kbranch/beefy_redox/STLs/LED Retainer.stl

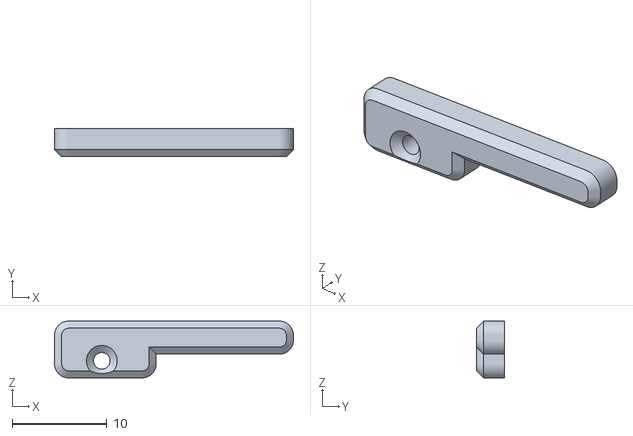
[picture p16: CAD file, 2020-09-06]
STLs/LED Retainer.stl
25.3 x 3.00 x 6.00
