kbranch/beefy_redox/STLs/Button Holder.stl

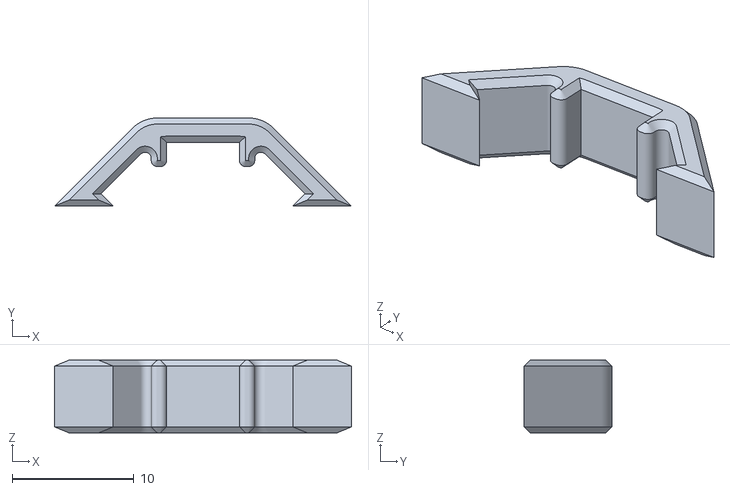
[picture p17: CAD file, 2020-09-06]
STLs/Button Holder.stl
24.4 x 7.25 x 6.00
