kbranch/beefy_redox/STLs/Keycaps/Keycap - 1.25U R3.stl

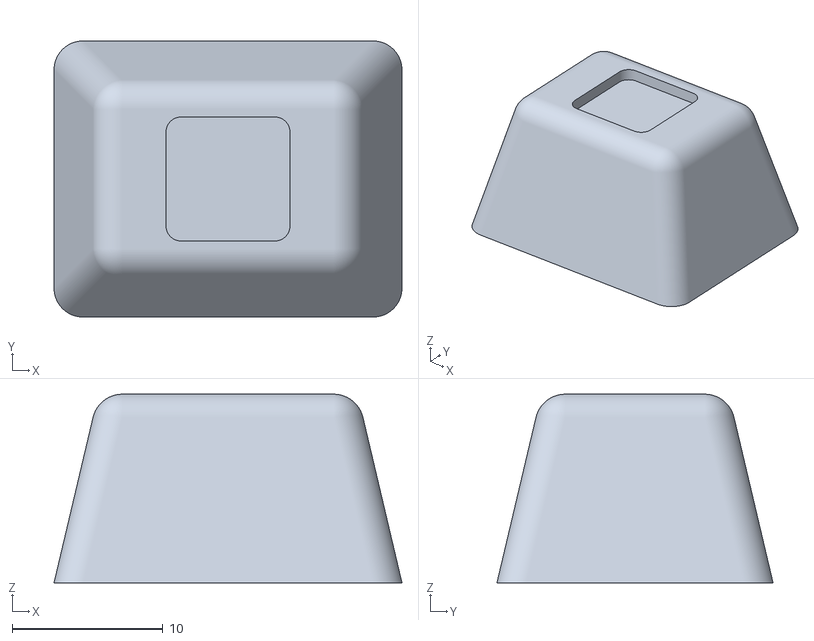
[picture p18: CAD file, 2020-09-06]
STLs/Keycaps/Keycap - 1.25U R3.stl
23.1 x 18.3 x 12.5
