kbranch/beefy_redox/STLs/Keycaps/Keycap - 1U R2.stl

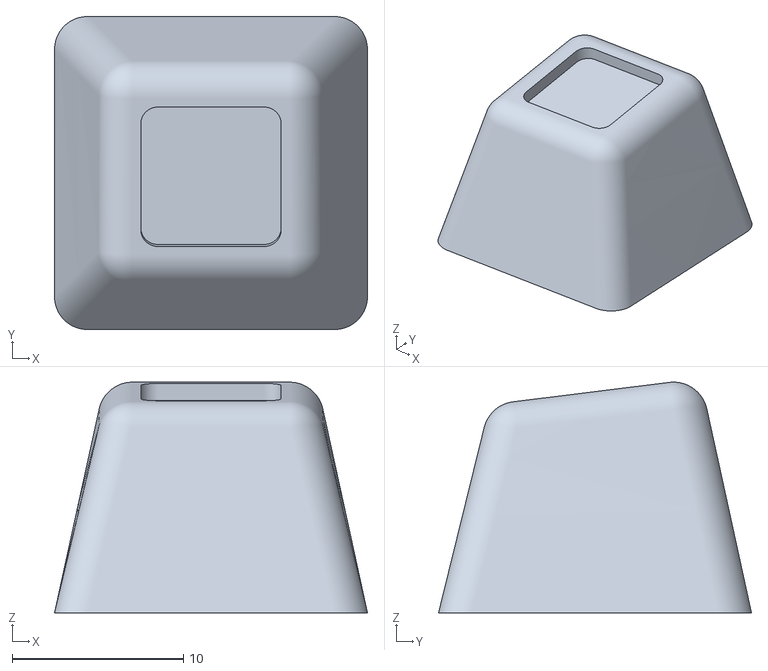
[picture p19: CAD file, 2020-09-06]
STLs/Keycaps/Keycap - 1U R2.stl
18.3 x 18.3 x 13.5
