kbranch/beefy_redox/STLs/Keycaps/Legends/Keycap - Legend Block - T.stl

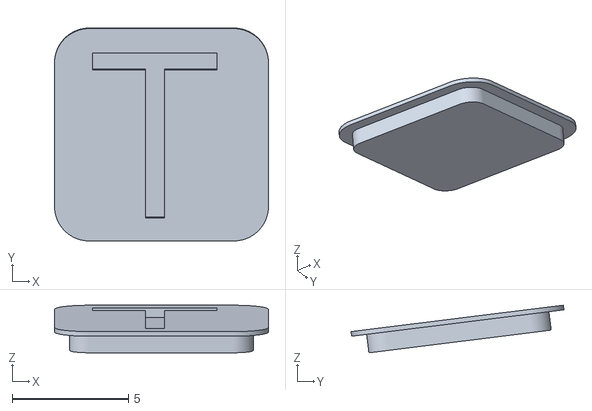
[picture p20: CAD file, 2020-09-06]
STLs/Keycaps/Legends/Keycap - Legend Block - T.stl
9.21 x 9.17 x 2.05
