kbranch/beefy_redox/STLs/Keycaps/Keycap - 1.5U R3.stl

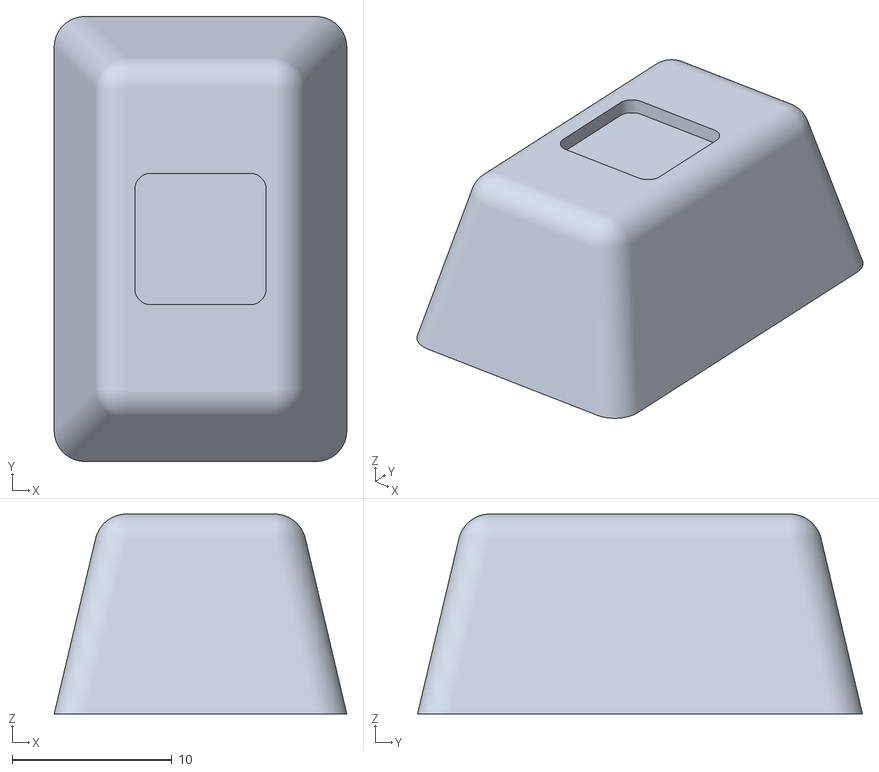
[picture p21: CAD file, 2020-09-06]
STLs/Keycaps/Keycap - 1.5U R3.stl
18.3 x 27.8 x 12.5
