kbranch/beefy_redox/STLs/Keycaps/Legends/Keycap - Part 5 - -.stl

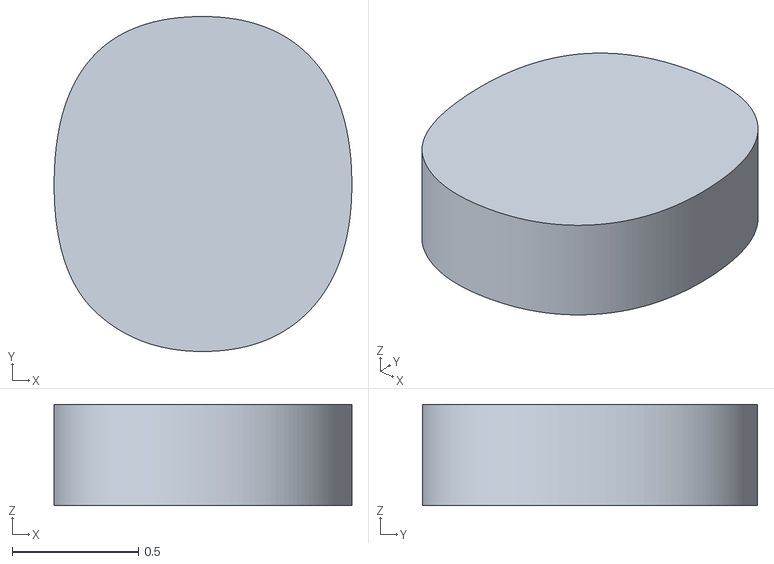
[picture p22: CAD file, 2020-09-06]
STLs/Keycaps/Legends/Keycap - Part 5 - -.stl
1.18 x 1.33 x 0.4
