kbranch/beefy_redox/STLs/Keycaps/Keycap - 1.25U R1.stl

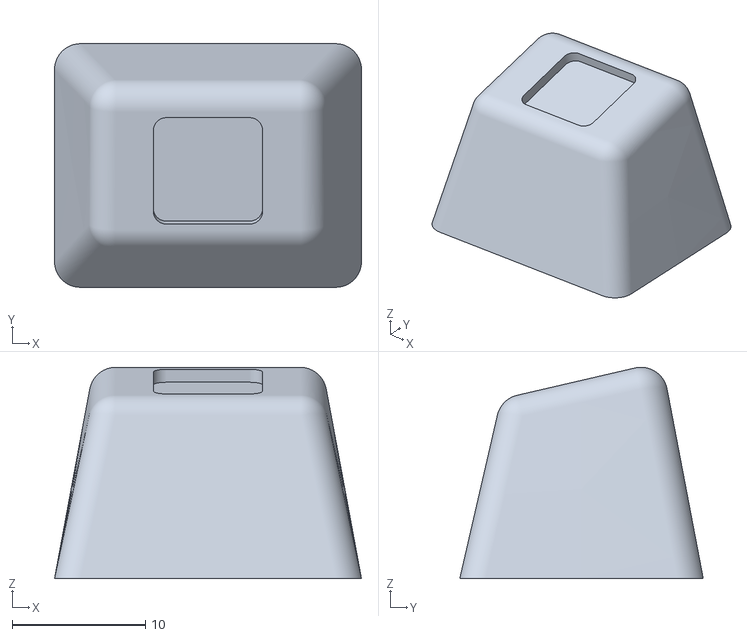
[picture p23: CAD file, 2020-09-06]
STLs/Keycaps/Keycap - 1.25U R1.stl
23.1 x 18.3 x 15.9
