kbranch/beefy_redox/STLs/Keycaps/Legends/Keycap - Part 3 - Space.stl

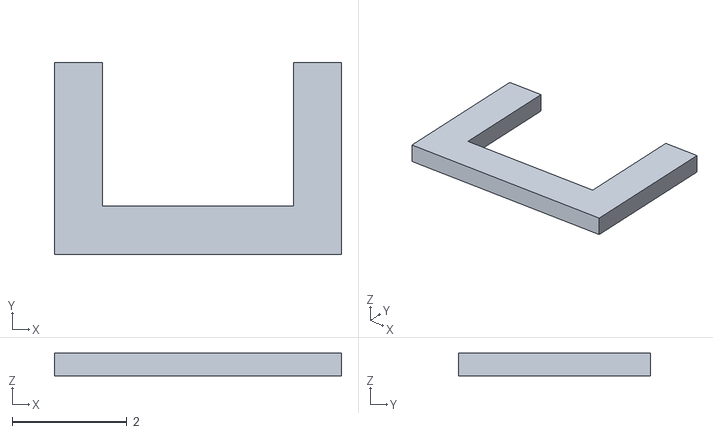
[picture p24: CAD file, 2020-09-06]
STLs/Keycaps/Legends/Keycap - Part 3 - Space.stl
5.00 x 3.34 x 0.4
