kbranch/beefy_redox/STLs/Keycaps/Legends/Keycap - Legend - 0.stl

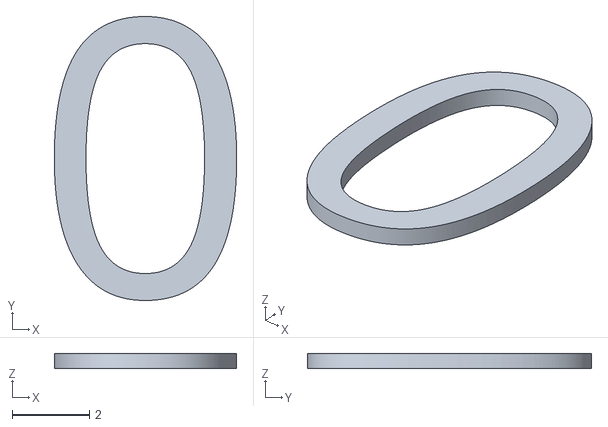
[picture p25: CAD file, 2020-09-06]
STLs/Keycaps/Legends/Keycap - Legend - 0.stl
4.73 x 7.36 x 0.4
