kbranch/beefy_redox/STLs/Keycaps/Legends/Keycap - Part 3 - Triangle.stl

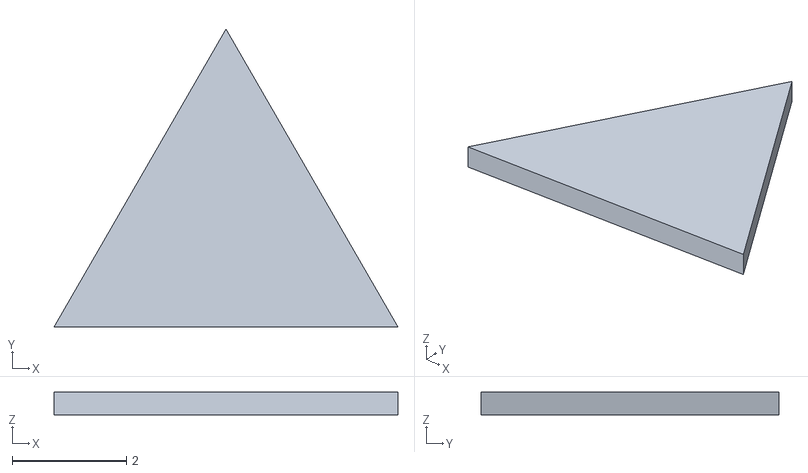
[picture p26: CAD file, 2020-09-06]
STLs/Keycaps/Legends/Keycap - Part 3 - Triangle.stl
6.02 x 5.21 x 0.4
