kbranch/beefy_redox/STLs/Keycaps/Legends/Keycap - Part 4 - Backslash.stl

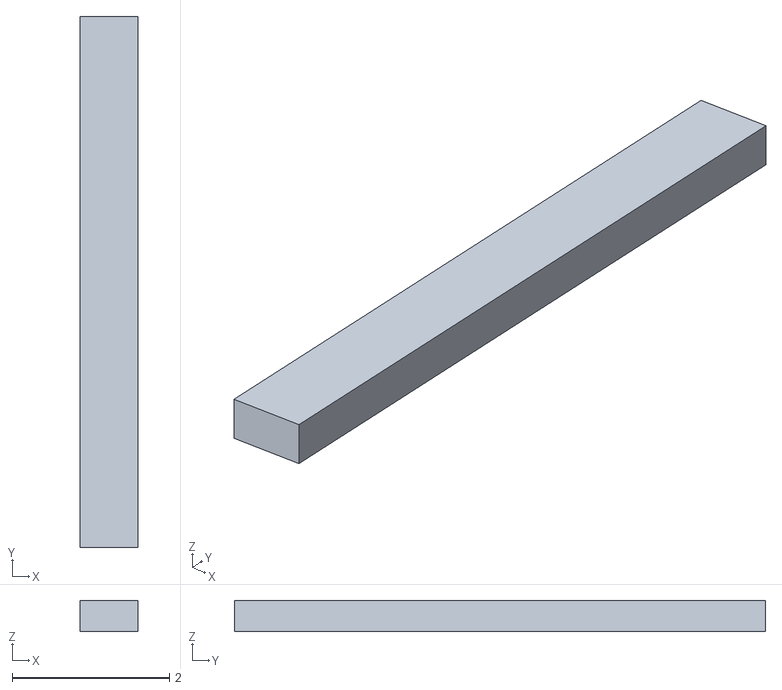
[picture p27: CAD file, 2020-09-06]
STLs/Keycaps/Legends/Keycap - Part 4 - Backslash.stl
0.733 x 6.74 x 0.4
