kbranch/beefy_redox/STLs/Keycaps/Legends/Keycap - Part 3 - Backspace.stl

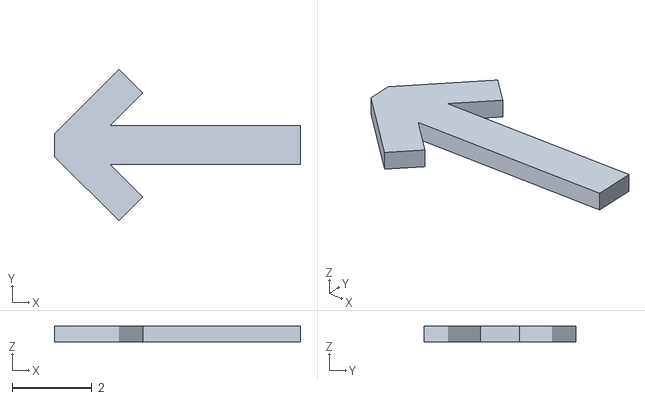
[picture p28: CAD file, 2020-09-06]
STLs/Keycaps/Legends/Keycap - Part 3 - Backspace.stl
6.18 x 3.82 x 0.4
