kbranch/beefy_redox/STLs/Keycaps/Legends/Keycap - Legend - Backslash.stl

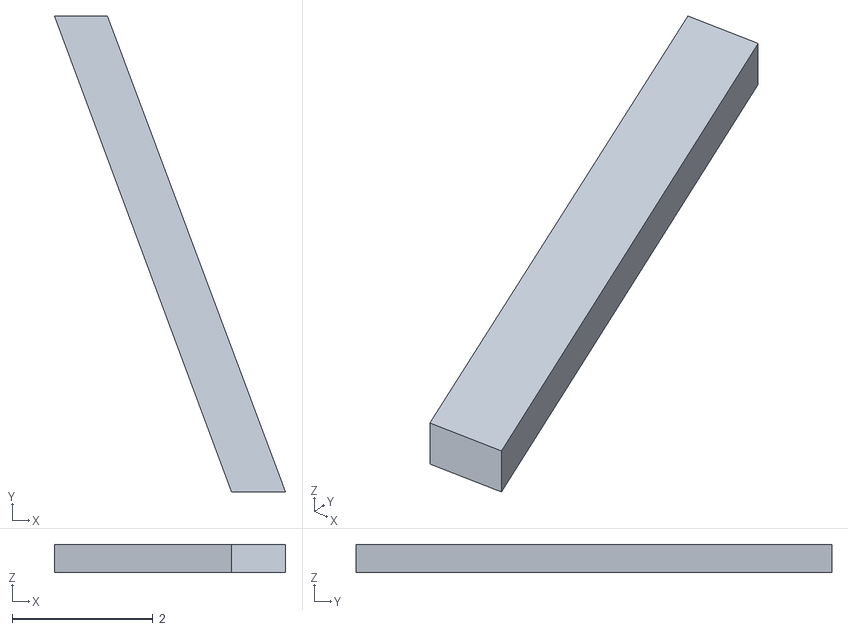
[picture p29: CAD file, 2020-09-06]
STLs/Keycaps/Legends/Keycap - Legend - Backslash.stl
3.28 x 6.75 x 0.4
