kbranch/beefy_redox/STLs/Keycaps/Legends/Keycap - Legend - S.stl

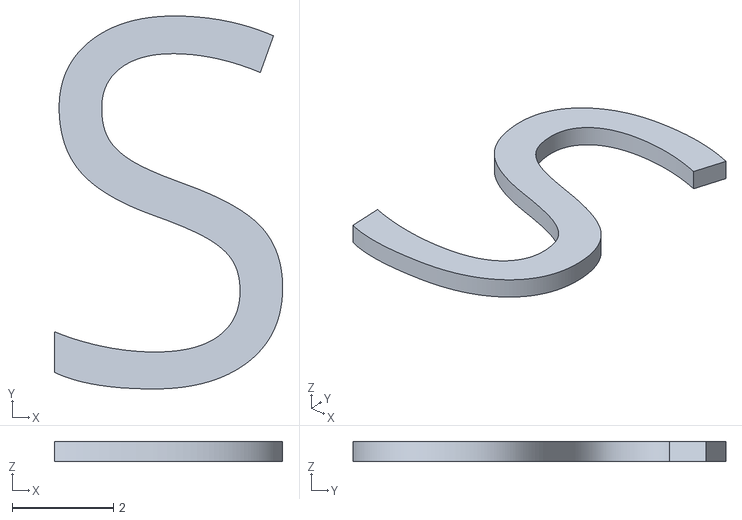
[picture p30: CAD file, 2020-09-06]
STLs/Keycaps/Legends/Keycap - Legend - S.stl
4.50 x 7.35 x 0.4
