kbranch/beefy_redox/STLs/Keycaps/Legends/Keycap - Legend - H.stl

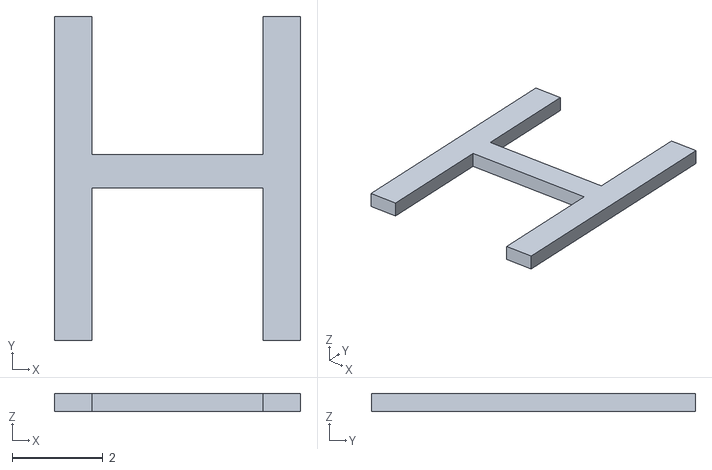
[picture p31: CAD file, 2020-09-06]
STLs/Keycaps/Legends/Keycap - Legend - H.stl
5.43 x 7.15 x 0.4
