kbranch/beefy_redox/STLs/Keycaps/Legends/Keycap - Part 3 - Circle.stl

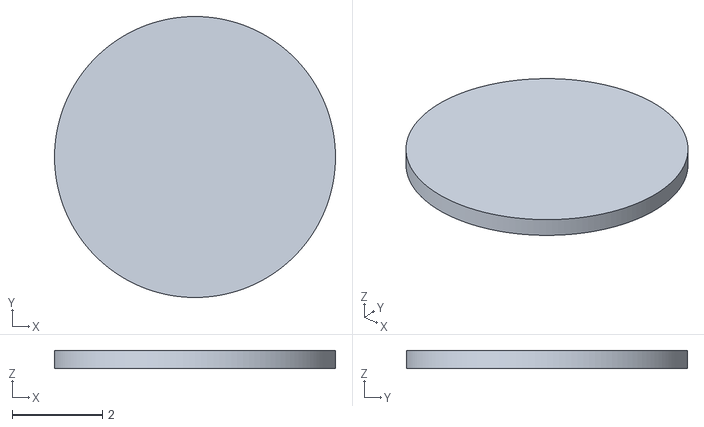
[picture p32: CAD file, 2020-09-06]
STLs/Keycaps/Legends/Keycap - Part 3 - Circle.stl
6.21 x 6.21 x 0.4
