kbranch/beefy_redox/STLs/Keycaps/Legends/Keycap - Part 4 - Win.stl

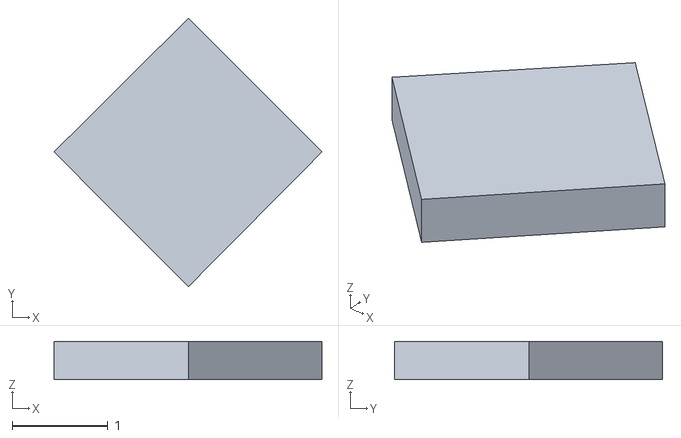
[picture p33: CAD file, 2020-09-06]
STLs/Keycaps/Legends/Keycap - Part 4 - Win.stl
2.79 x 2.80 x 0.4
