kbranch/beefy_redox/STLs/Keycaps/Legends/Keycap - Legend - M.stl

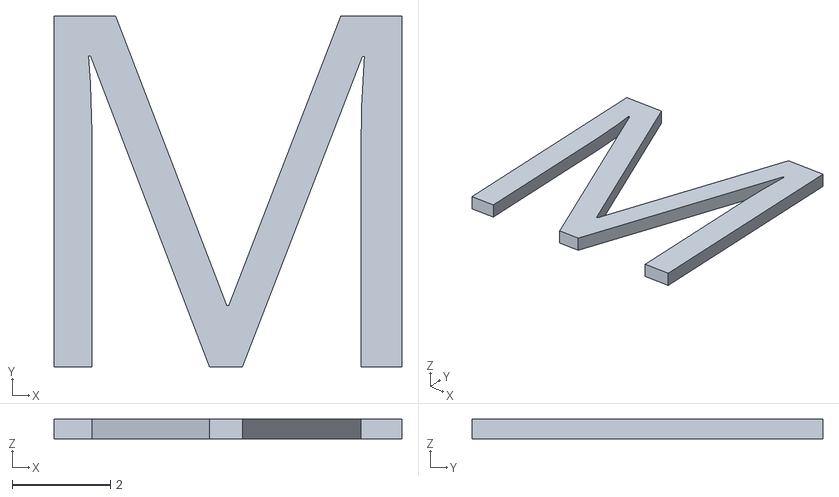
[picture p34: CAD file, 2020-09-06]
STLs/Keycaps/Legends/Keycap - Legend - M.stl
7.08 x 7.15 x 0.4
