kbranch/beefy_redox/STLs/Keycaps/Legends/Keycap - Legend - I.stl

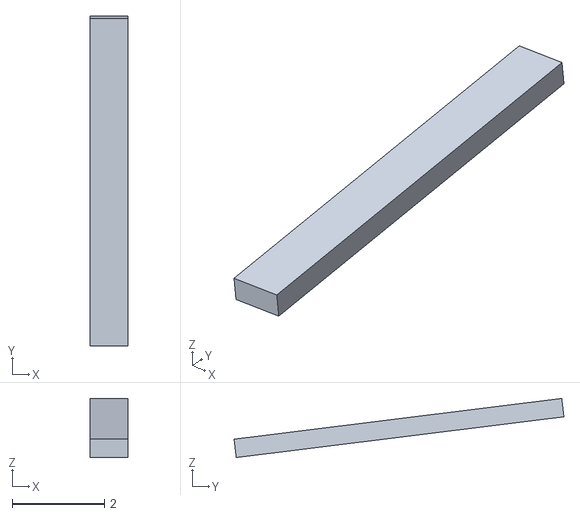
[picture p35: CAD file, 2020-09-06]
STLs/Keycaps/Legends/Keycap - Legend - I.stl
0.831 x 7.15 x 1.28
