kbranch/beefy_redox/STLs/Keycaps/Legends/Keycap - Legend - A.stl

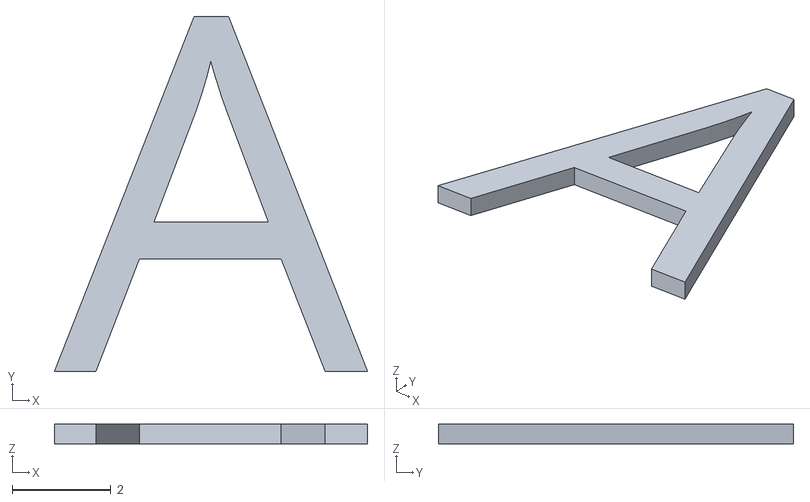
[picture p36: CAD file, 2020-09-06]
STLs/Keycaps/Legends/Keycap - Legend - A.stl
6.34 x 7.18 x 0.4
