kbranch/beefy_redox/STLs/Keycaps/Legends/Keycap - Legend - N.stl

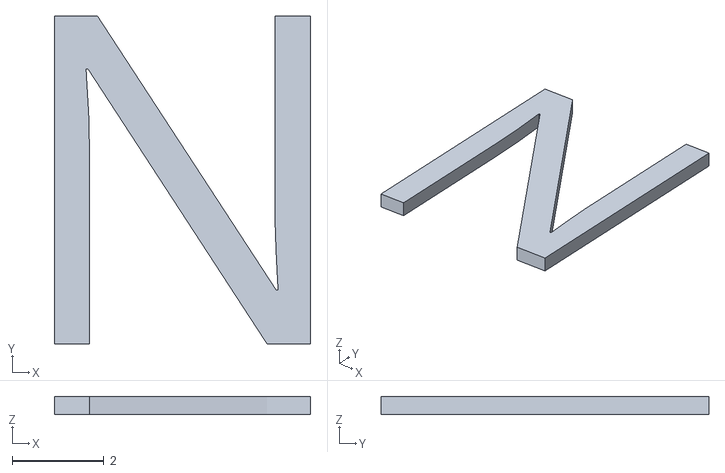
[picture p37: CAD file, 2020-09-06]
STLs/Keycaps/Legends/Keycap - Legend - N.stl
5.59 x 7.15 x 0.4
