kbranch/beefy_redox/STLs/Keycaps/Legends/Keycap - Part 3 - UpRight.stl

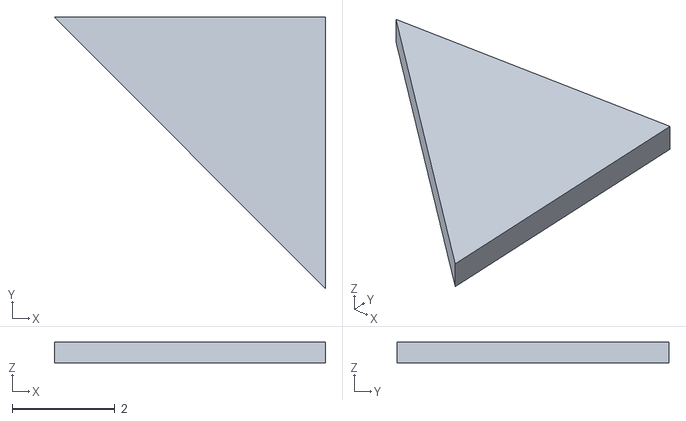
[picture p38: CAD file, 2020-09-06]
STLs/Keycaps/Legends/Keycap - Part 3 - UpRight.stl
5.27 x 5.29 x 0.4
