kbranch/beefy_redox/STLs/Keycaps/Legends/Keycap - Legend - B.stl

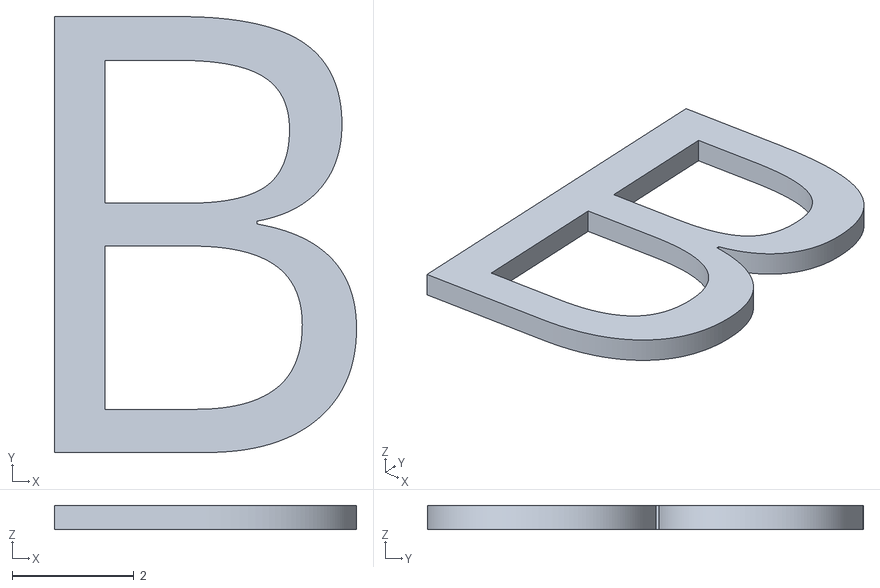
[picture p39: CAD file, 2020-09-06]
STLs/Keycaps/Legends/Keycap - Legend - B.stl
4.96 x 7.15 x 0.4
