kbranch/beefy_redox/STLs/Keycaps/Legends/Keycap - Legend - U.stl

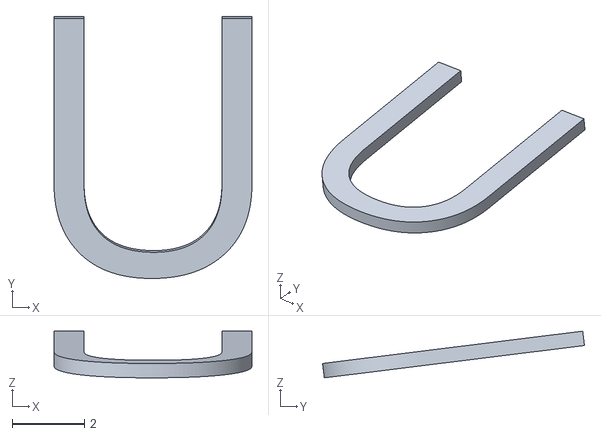
[picture p40: CAD file, 2020-09-06]
STLs/Keycaps/Legends/Keycap - Legend - U.stl
5.47 x 7.25 x 1.29
