kbranch/beefy_redox/STLs/Keycaps/Legends/Keycap - Part 4 - ,.stl

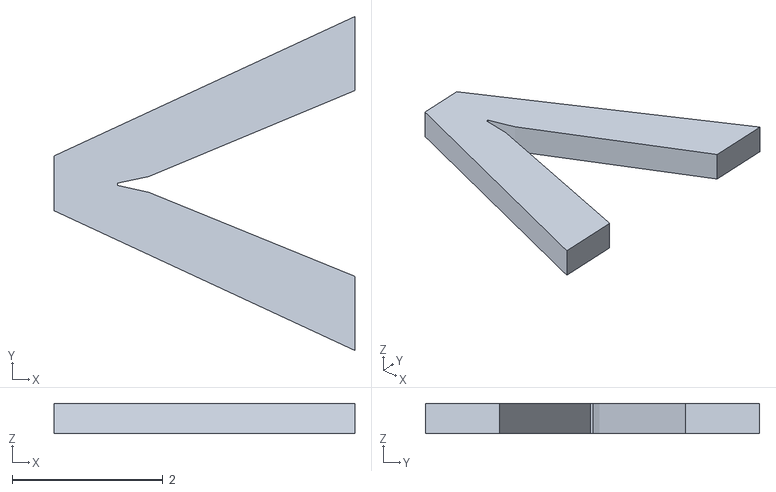
[picture p41: CAD file, 2020-09-06]
STLs/Keycaps/Legends/Keycap - Part 4 - ,.stl
3.99 x 4.43 x 0.4
