kbranch/beefy_redox/STLs/Keycaps/Legends/Keycap - Legend - K.stl

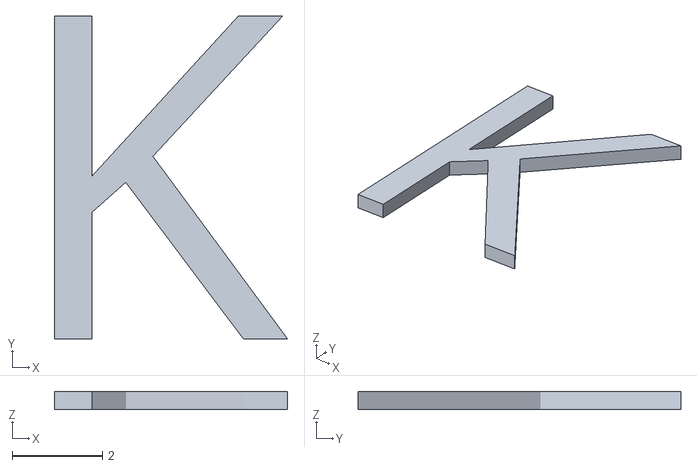
[picture p42: CAD file, 2020-09-06]
STLs/Keycaps/Legends/Keycap - Legend - K.stl
5.17 x 7.15 x 0.4
