kbranch/beefy_redox/STLs/Keycaps/Legends/Keycap - Legend - 5.stl

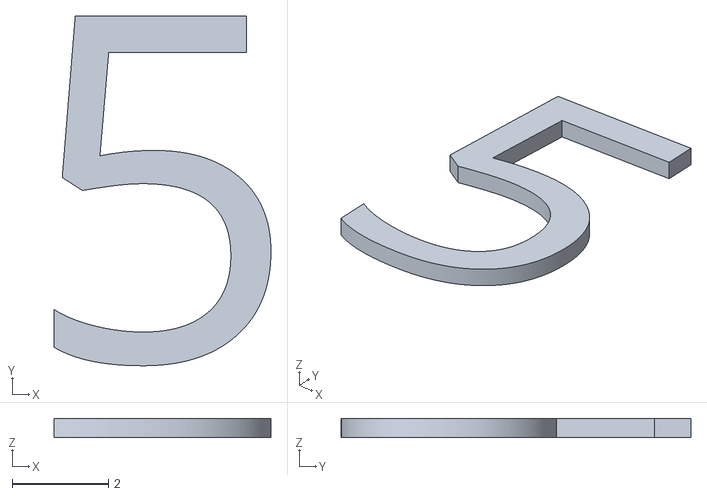
[picture p43: CAD file, 2020-09-06]
STLs/Keycaps/Legends/Keycap - Legend - 5.stl
4.50 x 7.25 x 0.4
