kbranch/beefy_redox/STLs/Keycaps/Legends/Keycap - Legend - J.stl

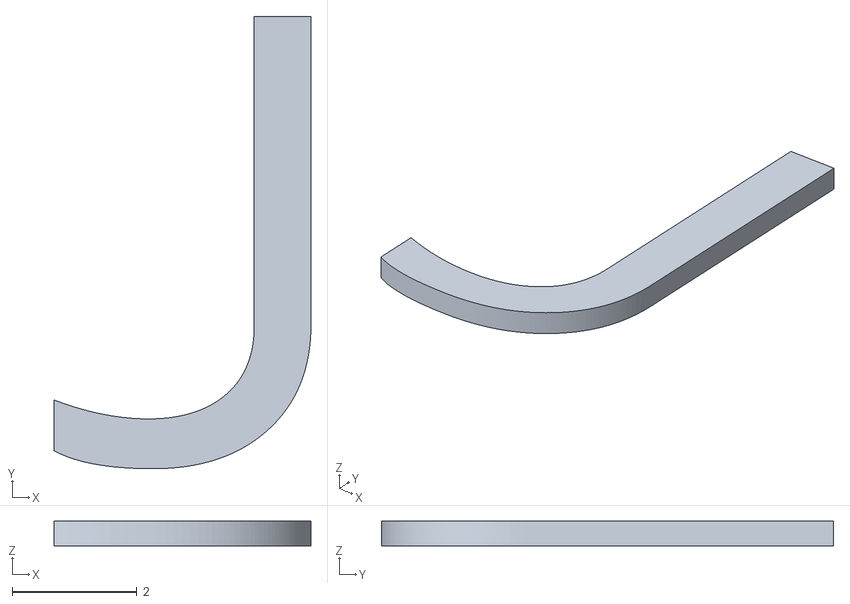
[picture p44: CAD file, 2020-09-06]
STLs/Keycaps/Legends/Keycap - Legend - J.stl
4.12 x 7.25 x 0.4
