kbranch/beefy_redox/STLs/Keycaps/Legends/Keycap - Legend - O.stl

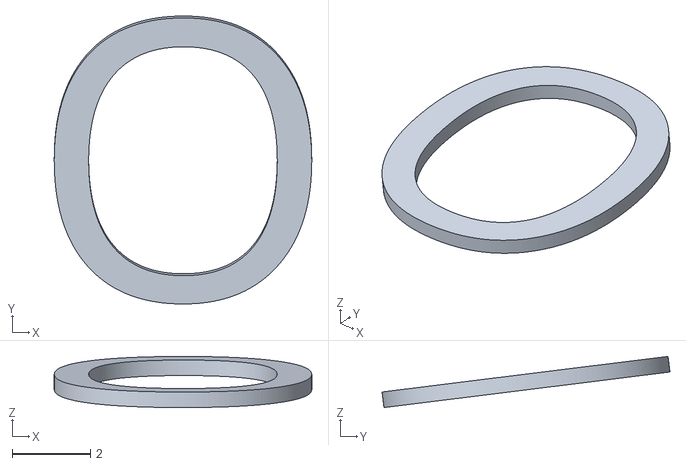
[picture p46: CAD file, 2020-09-06]
STLs/Keycaps/Legends/Keycap - Legend - O.stl
6.58 x 7.36 x 1.31
