kbranch/beefy_redox/STLs/Keycaps/Legends/Keycap - Legend - R.stl

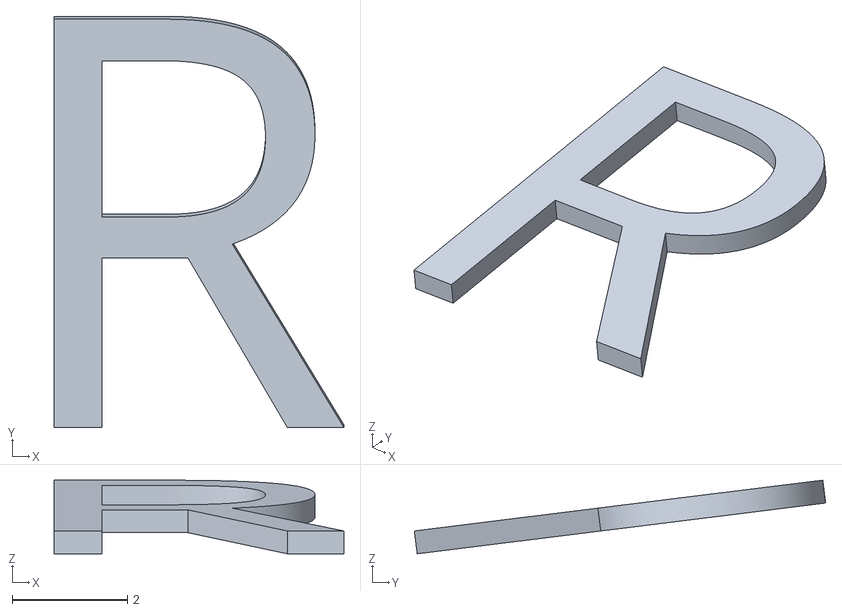
[picture p47: CAD file, 2020-09-06]
STLs/Keycaps/Legends/Keycap - Legend - R.stl
5.04 x 7.15 x 1.28
