kbranch/beefy_redox/STLs/Keycaps/Legends/Keycap - Legend - G.stl

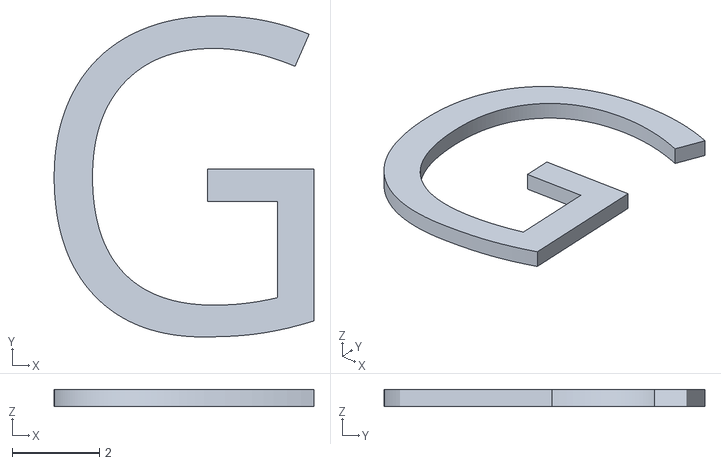
[picture p48: CAD file, 2020-09-06]
STLs/Keycaps/Legends/Keycap - Legend - G.stl
5.95 x 7.35 x 0.4
