kbranch/beefy_redox/STLs/Keycaps/Legends/Keycap - Legend - C.stl

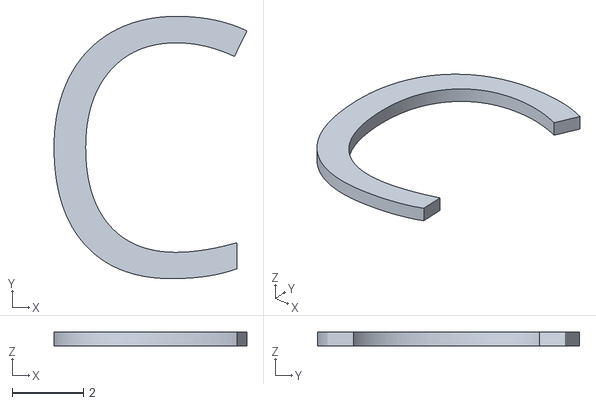
[picture p49: CAD file, 2020-09-06]
STLs/Keycaps/Legends/Keycap - Legend - C.stl
5.41 x 7.35 x 0.4
