kbranch/beefy_redox/STLs/Keycaps/Legends/Keycap - Legend - W.stl

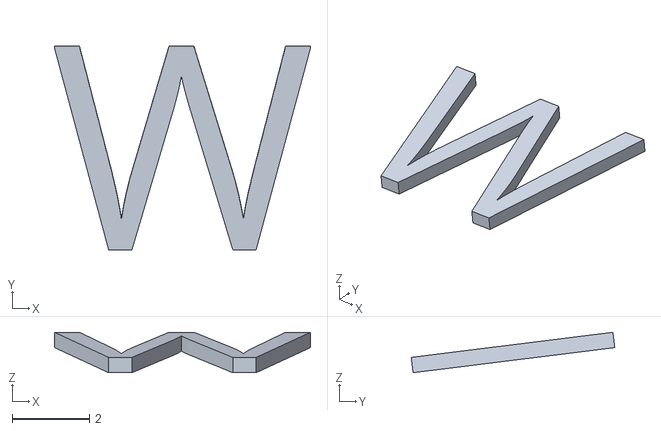
[picture p50: CAD file, 2020-09-06]
STLs/Keycaps/Legends/Keycap - Legend - W.stl
6.64 x 5.28 x 1.05
