kbranch/beefy_redox/STLs/Keycaps/Legends/Keycap - Legend - '-.stl

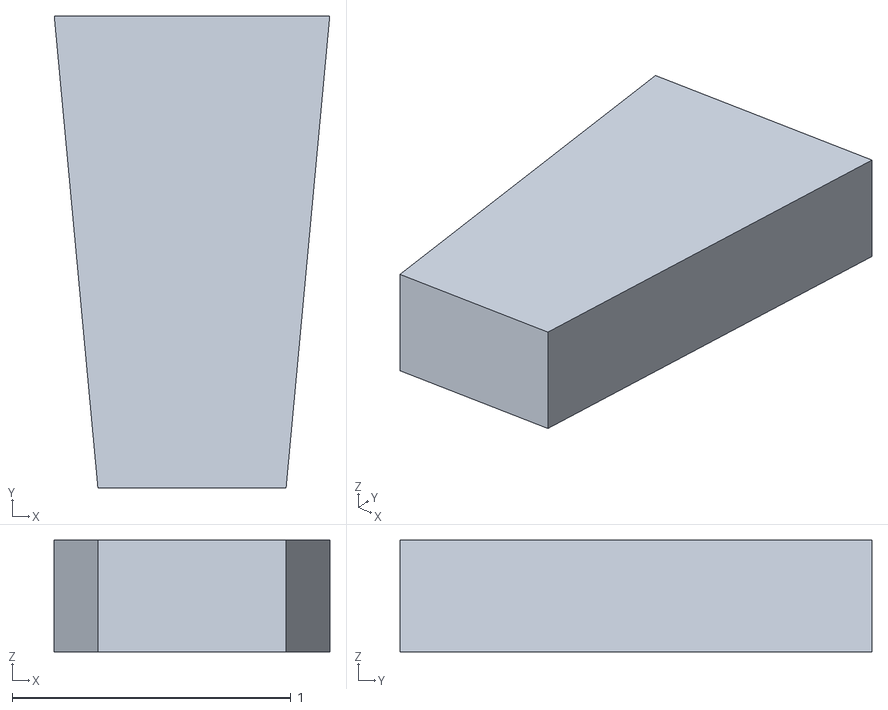
[picture p51: CAD file, 2020-09-06]
STLs/Keycaps/Legends/Keycap - Legend - '-.stl
0.988 x 1.69 x 0.4
