kbranch/beefy_redox/STLs/Keycaps/Legends/Keycap - Part 3 - Tab.stl

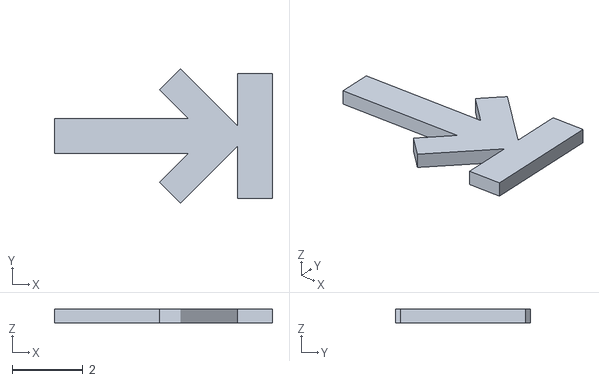
[picture p52: CAD file, 2020-09-06]
STLs/Keycaps/Legends/Keycap - Part 3 - Tab.stl
6.18 x 3.82 x 0.4
