kbranch/beefy_redox/STLs/Keycaps/Legends/Keycap - Legend - V.stl

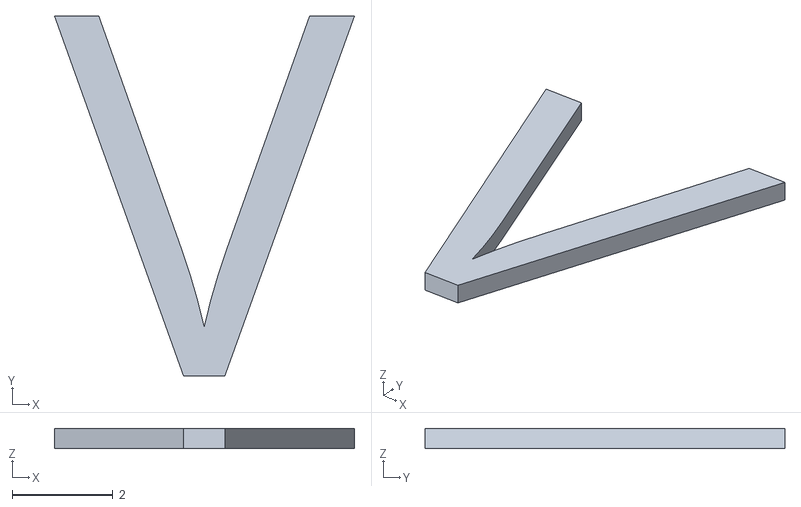
[picture p53: CAD file, 2020-09-06]
STLs/Keycaps/Legends/Keycap - Legend - V.stl
5.96 x 7.15 x 0.4
