kbranch/beefy_redox/STLs/Keycaps/Legends/Keycap - Legend - E.stl

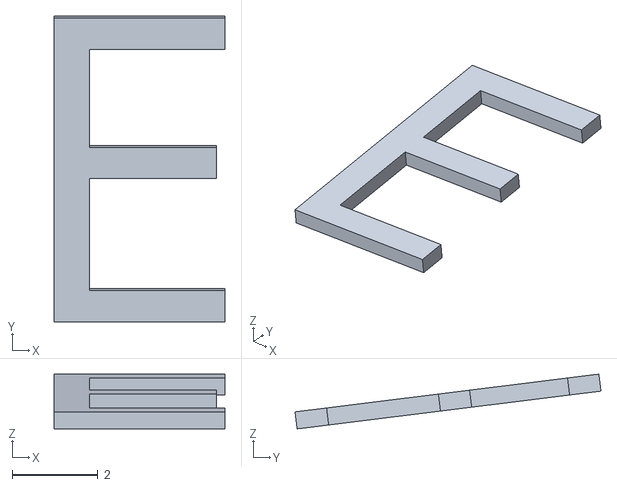
[picture p54: CAD file, 2020-09-06]
STLs/Keycaps/Legends/Keycap - Legend - E.stl
3.99 x 7.15 x 1.28
