kbranch/beefy_redox/STLs/Keycaps/Legends/Keycap - Part 3 - Diamond.stl

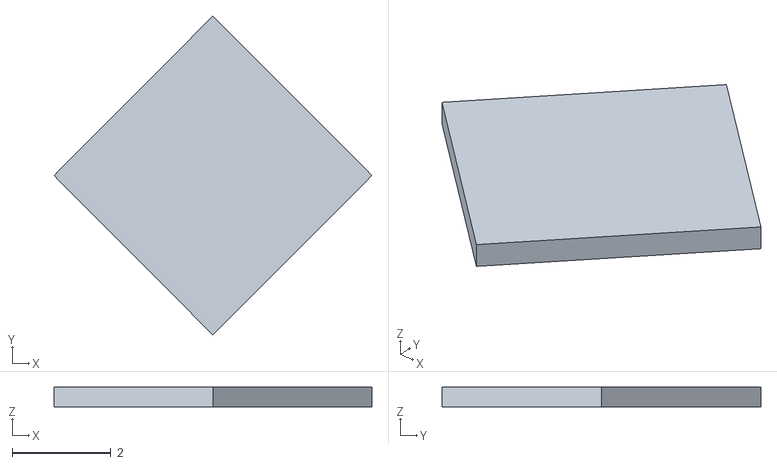
[picture p55: CAD file, 2020-09-06]
STLs/Keycaps/Legends/Keycap - Part 3 - Diamond.stl
6.44 x 6.46 x 0.4
