kbranch/beefy_redox/STLs/Keycaps/Legends/Keycap - Legend - D.stl

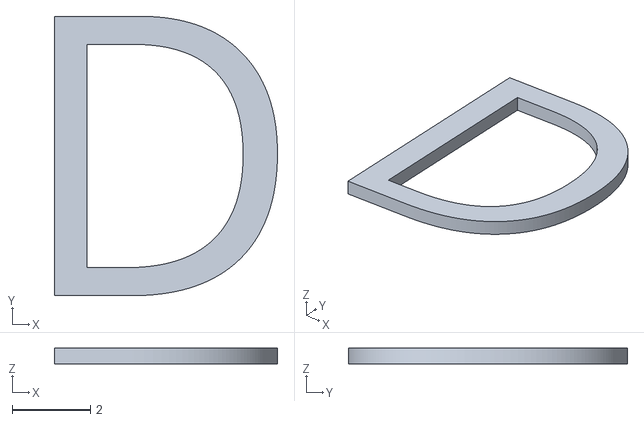
[picture p56: CAD file, 2020-09-06]
STLs/Keycaps/Legends/Keycap - Legend - D.stl
5.71 x 7.15 x 0.4
