kbranch/beefy_redox/STLs/Keycaps/Legends/Keycap - Part 3 - Return.stl

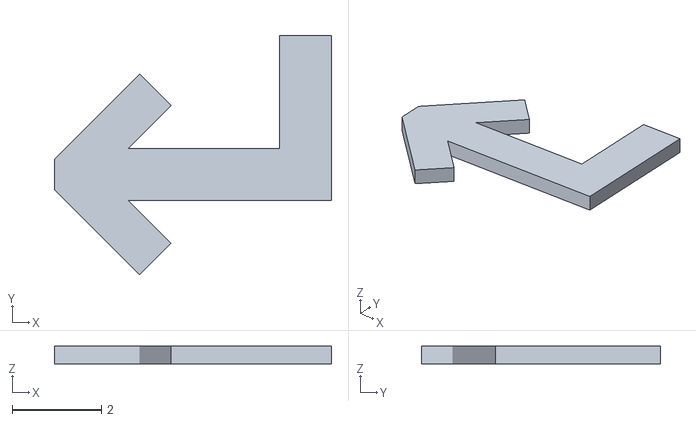
[picture p57: CAD file, 2020-09-06]
STLs/Keycaps/Legends/Keycap - Part 3 - Return.stl
6.22 x 5.38 x 0.4
