kbranch/beefy_redox/STLs/Keycaps/Legends/Keycap - Legend - 7.stl

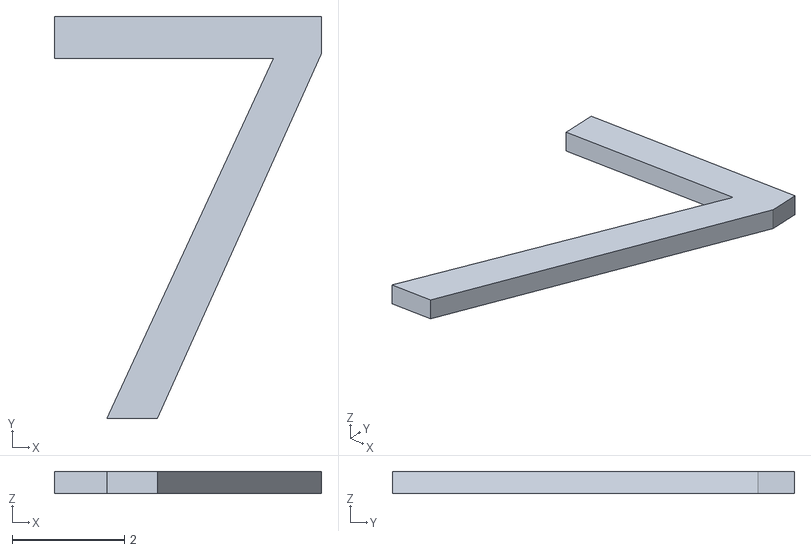
[picture p58: CAD file, 2020-09-06]
STLs/Keycaps/Legends/Keycap - Legend - 7.stl
4.76 x 7.15 x 0.4
