kbranch/beefy_redox/STLs/Keycaps/Legends/Keycap - Legend Block - I.stl

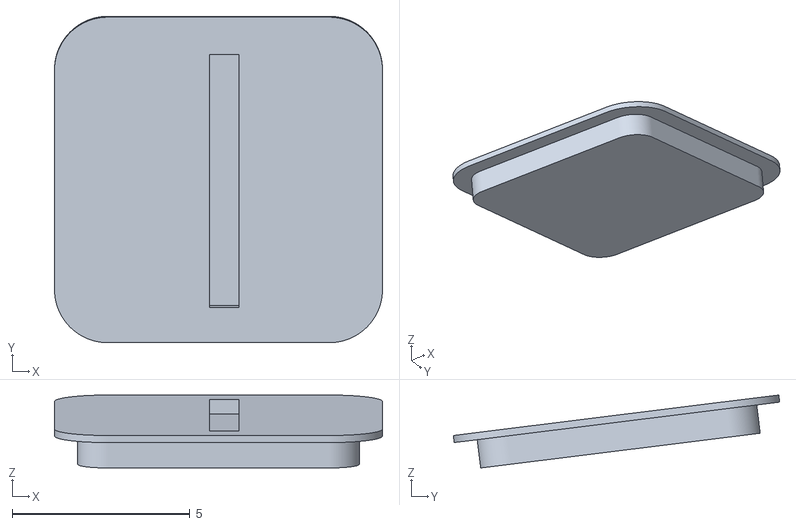
[picture p59: CAD file, 2020-09-06]
STLs/Keycaps/Legends/Keycap - Legend Block - I.stl
9.21 x 9.17 x 2.05
