kbranch/beefy_redox/STLs/Keycaps/Legends/Keycap - Part 3 - Parallelogram.stl

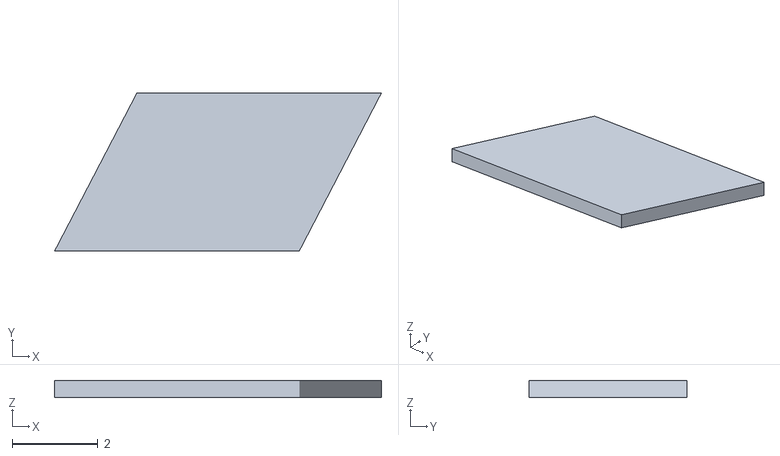
[picture p60: CAD file, 2020-09-06]
STLs/Keycaps/Legends/Keycap - Part 3 - Parallelogram.stl
7.61 x 3.68 x 0.4
