kbranch/beefy_redox/STLs/Keycaps/Legends/Keycap - Legend - X.stl

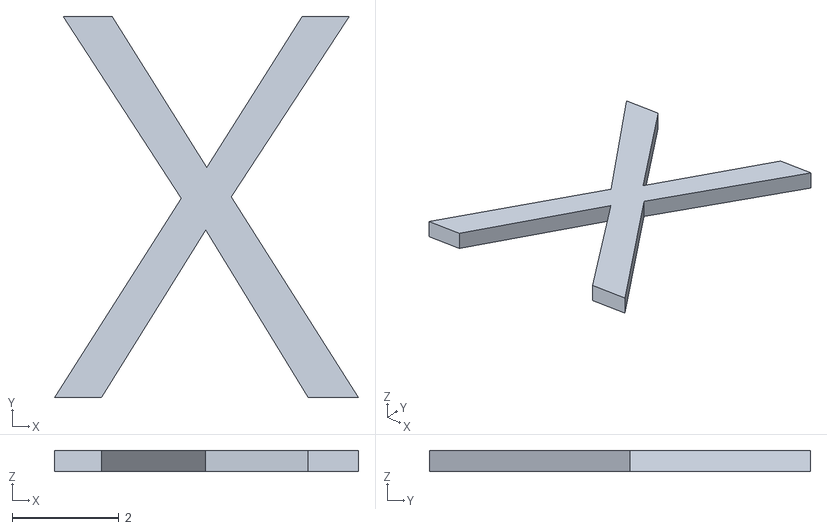
[picture p61: CAD file, 2020-09-06]
STLs/Keycaps/Legends/Keycap - Legend - X.stl
5.70 x 7.15 x 0.4
