kbranch/beefy_redox/STLs/Keycaps/Legends/Keycap - Legend - P.stl

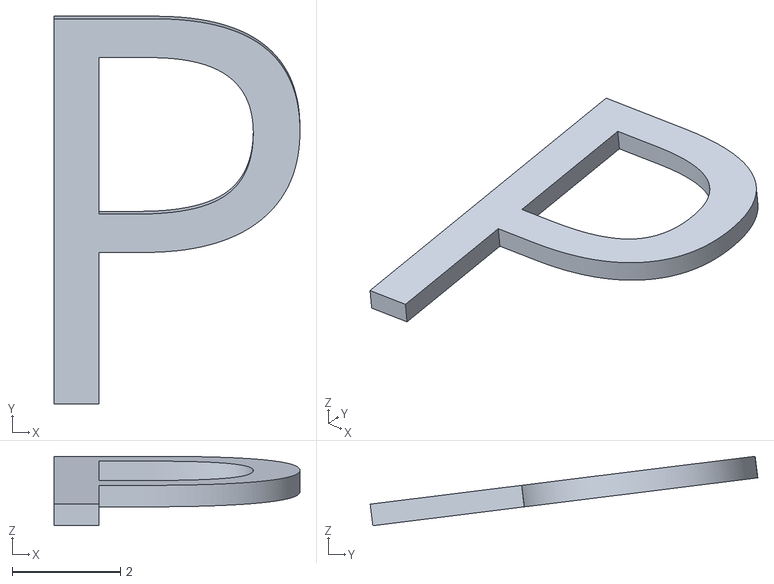
[picture p62: CAD file, 2020-09-06]
STLs/Keycaps/Legends/Keycap - Legend - P.stl
4.54 x 7.15 x 1.28
