kbranch/beefy_redox/STLs/Keycaps/Legends/Keycap - Legend - T.stl

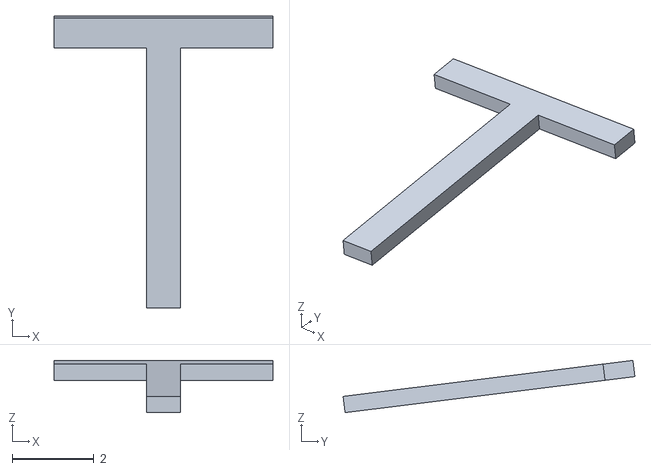
[picture p63: CAD file, 2020-09-06]
STLs/Keycaps/Legends/Keycap - Legend - T.stl
5.36 x 7.15 x 1.28
