kbranch/beefy_redox/STLs/Keycaps/Legends/Keycap - Legend Block - M.stl

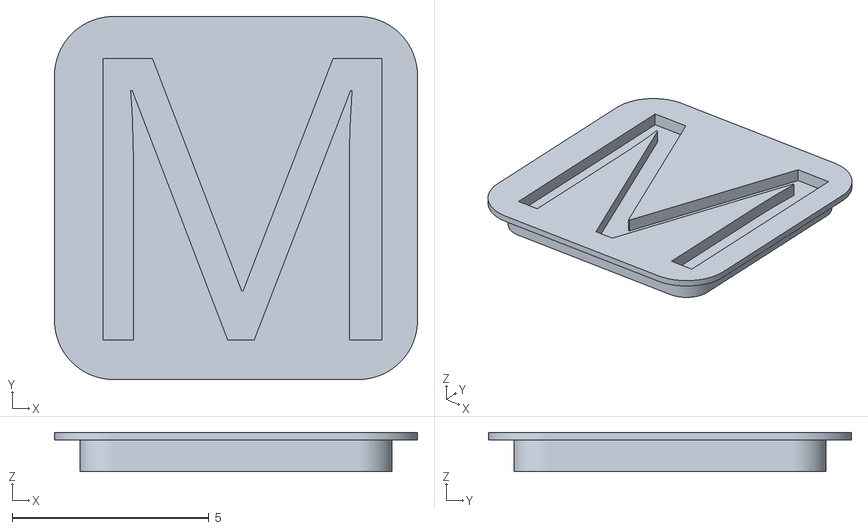
[picture p64: CAD file, 2020-09-06]
STLs/Keycaps/Legends/Keycap - Legend Block - M.stl
9.21 x 9.21 x 1.00
