kbranch/beefy_redox/STLs/Keycaps/Legends/Keycap - Part 3 - Asterisk.stl

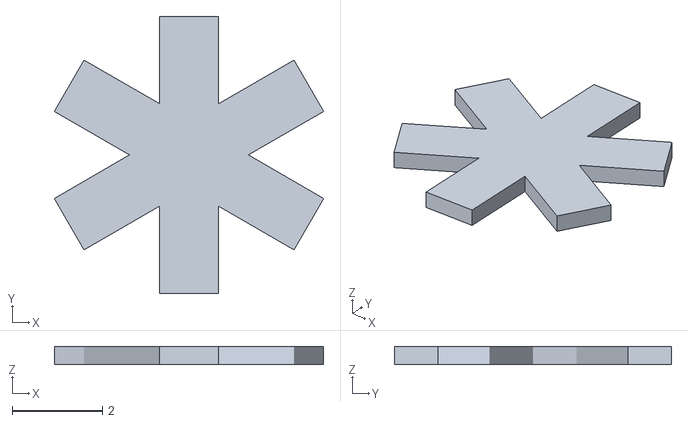
[picture p65: CAD file, 2020-09-06]
STLs/Keycaps/Legends/Keycap - Part 3 - Asterisk.stl
5.98 x 6.15 x 0.4
