kbranch/beefy_redox/STLs/Keycaps/Legends/Keycap - Legend - Ctrl.stl

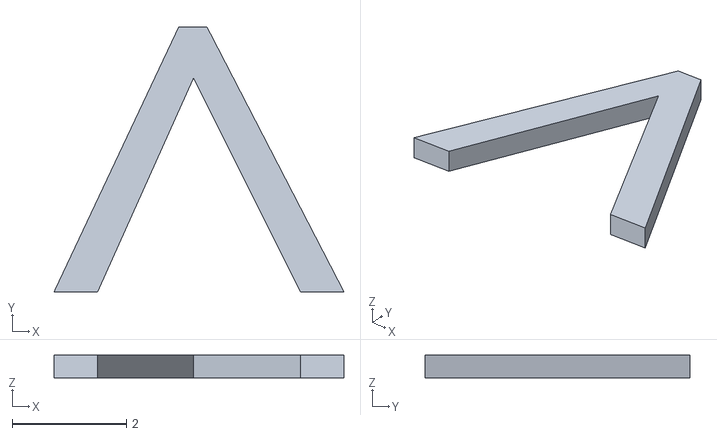
[picture p66: CAD file, 2020-09-06]
STLs/Keycaps/Legends/Keycap - Legend - Ctrl.stl
5.08 x 4.64 x 0.4
