kbranch/beefy_redox/STLs/Keycaps/Legends/Keycap - Legend - L.stl

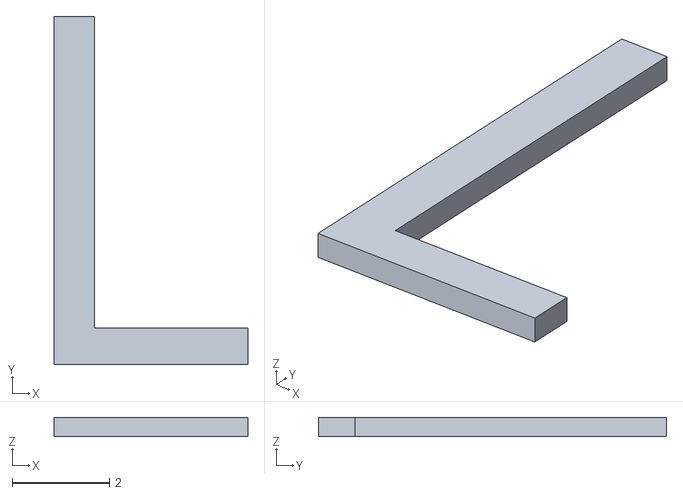
[picture p67: CAD file, 2020-09-06]
STLs/Keycaps/Legends/Keycap - Legend - L.stl
3.99 x 7.15 x 0.4
