kbranch/beefy_redox/STLs/Keycaps/Legends/Keycap - Legend - Z.stl

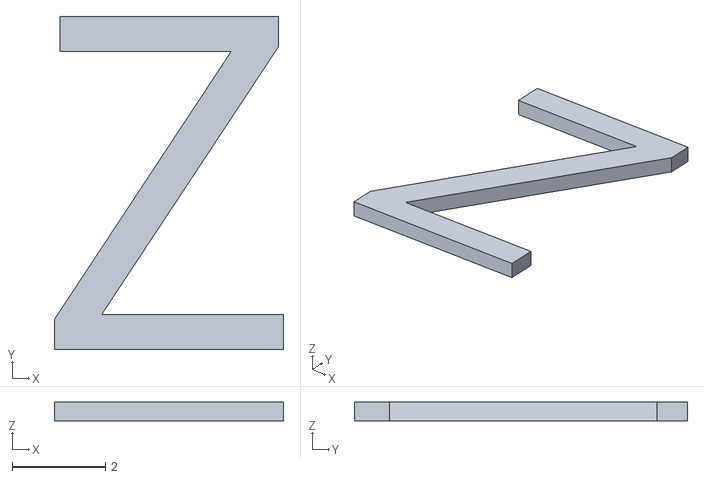
[picture p68: CAD file, 2020-09-06]
STLs/Keycaps/Legends/Keycap - Legend - Z.stl
4.92 x 7.15 x 0.4
